PankajaBalasooriya/SLRC-2025-Pulztrones/Designs/3D Prints/Part P.STL

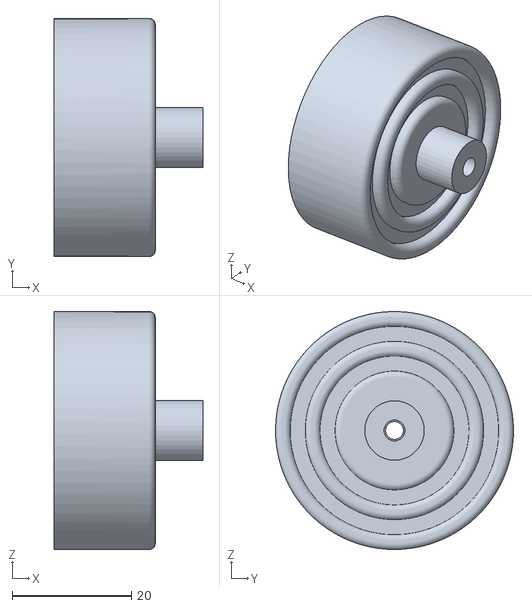
[picture p26: CAD file, 2025-03-19]
Designs/3D Prints/Part P.STL
25.0 x 40.0 x 40.0
