PankajaBalasooriya/SLRC-2025-Pulztrones/Designs/Laser Cuts/Bottom-plate.DXF

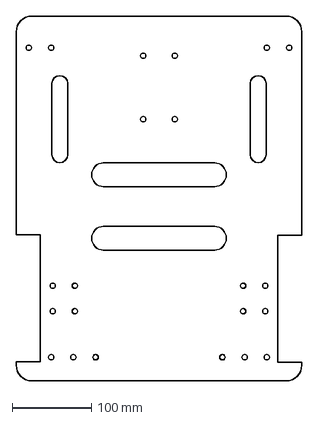
[picture p27: CAD file, 2025-03-19]
Designs/Laser Cuts/Bottom-plate.DXF
360.0 x 460.0 mm
