PankajaBalasooriya/SLRC-2025-Pulztrones/Designs/Mian Design/Bottom Base Plate.SLDPRT

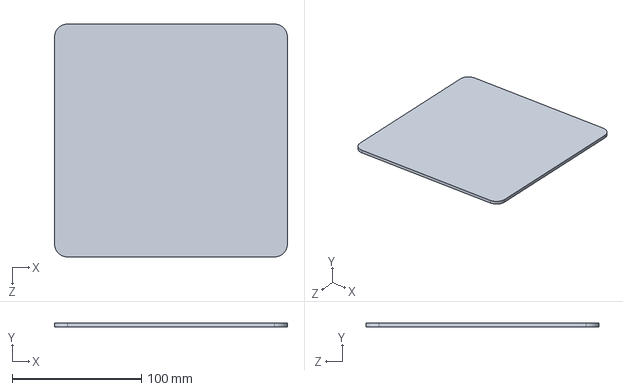
[picture p28: CAD file, 2025-03-19]
Designs/Mian Design/Bottom Base Plate.SLDPRT
180.0 x 3.00 x 180.0 mm
