PankajaBalasooriya/SLRC-2025-Pulztrones/Designs/Arm design/Part1.SLDPRT

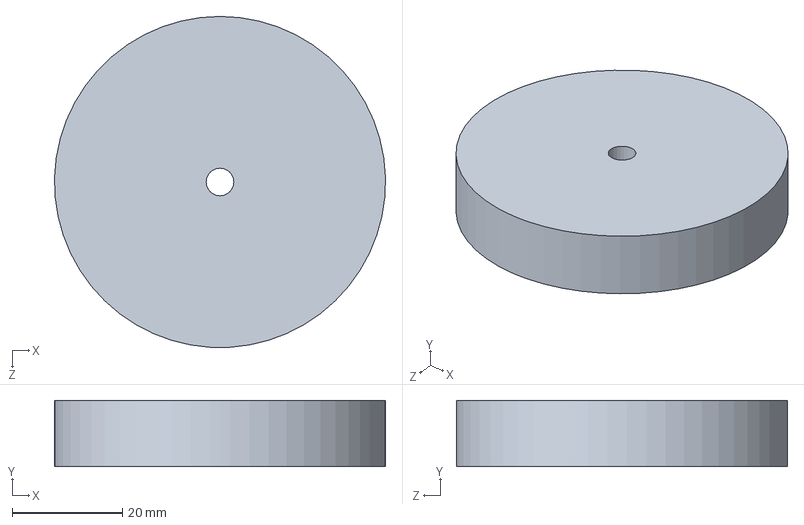
[picture p29: CAD file, 2025-03-19]
Designs/Arm design/Part1.SLDPRT
60.0 x 12.0 x 60.0 mm
