PankajaBalasooriya/SLRC-2025-Pulztrones/Designs/Laser Cuts/Mid-plate.DXF

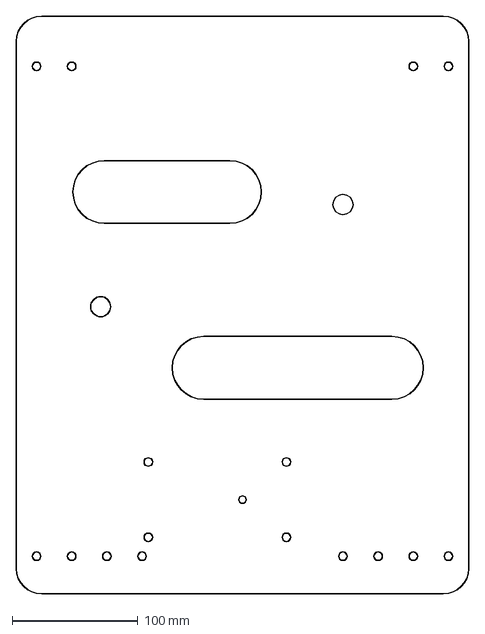
[picture p30: CAD file, 2025-03-19]
Designs/Laser Cuts/Mid-plate.DXF
360.0 x 460.0 mm
