PankajaBalasooriya/SLRC-2025-Pulztrones/Designs/Mian Design/Mid-plate.SLDPRT

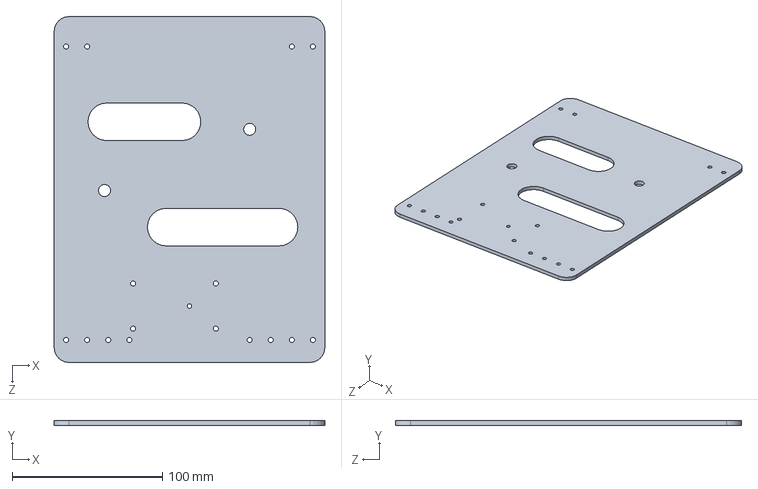
[picture p31: CAD file, 2025-03-19]
Designs/Mian Design/Mid-plate.SLDPRT
180.0 x 3.00 x 230.0 mm
