PankajaBalasooriya/SLRC-2025-Pulztrones/Designs/3D Prints/small servo mount.STL

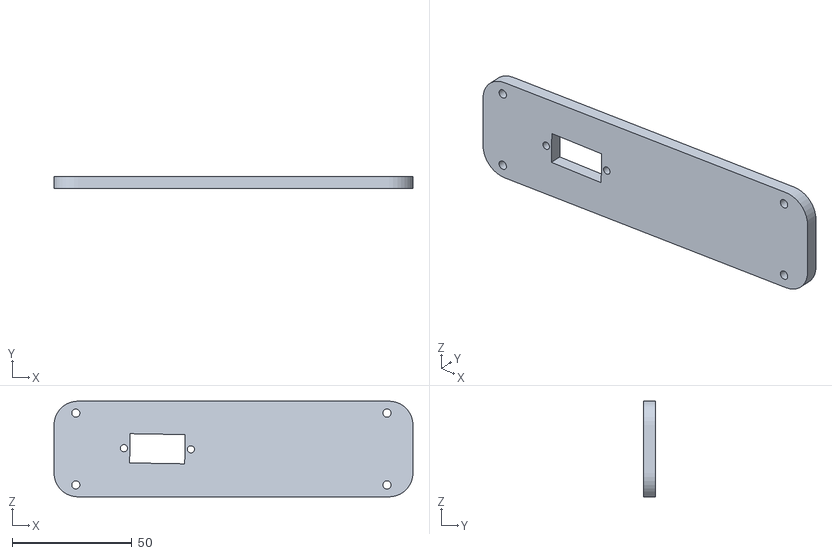
[picture p32: CAD file, 2025-03-19]
Designs/3D Prints/small servo mount.STL
150.0 x 5.00 x 40.0
