PankajaBalasooriya/SLRC-2025-Pulztrones/Designs/Arm design/part B.SLDPRT

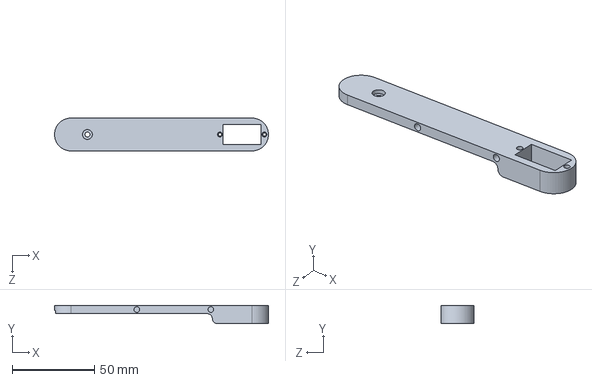
[picture p33: CAD file, 2025-03-19]
Designs/Arm design/part B.SLDPRT
130.0 x 11.0 x 20.0 mm
