PankajaBalasooriya/SLRC-2025-Pulztrones/Designs/Arm design/Part J.SLDPRT

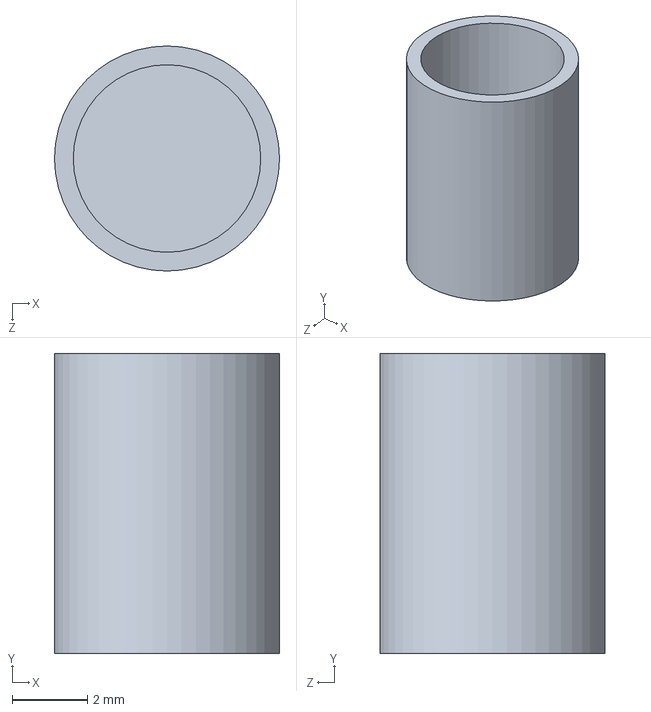
[picture p35: CAD file, 2025-03-19]
Designs/Arm design/Part J.SLDPRT
6.00 x 8.00 x 6.00 mm
