PankajaBalasooriya/SLRC-2025-Pulztrones/Designs/Mian Design/Top-plate.SLDPRT

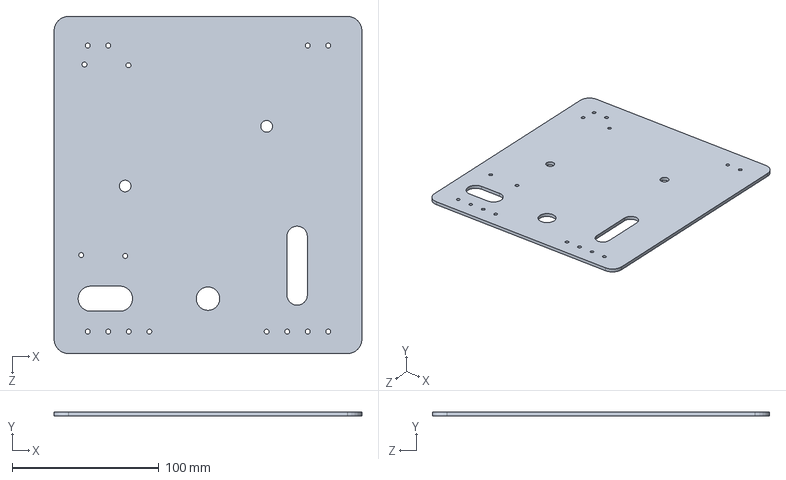
[picture p36: CAD file, 2025-03-19]
Designs/Mian Design/Top-plate.SLDPRT
210.0 x 3.00 x 230.0 mm
