PankajaBalasooriya/SLRC-2025-Pulztrones/Designs/Arm design/big servo holder.SLDPRT

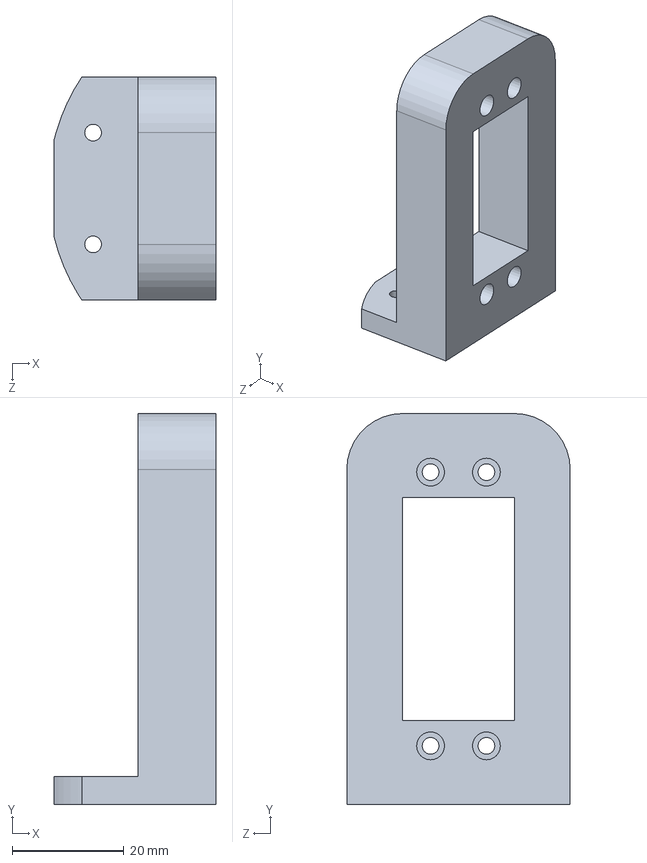
[picture p37: CAD file, 2025-03-19]
Designs/Arm design/big servo holder.SLDPRT
29.0 x 70.0 x 40.0 mm
