PankajaBalasooriya/SLRC-2025-Pulztrones/Designs/Mian Design/mid low plate.SLDPRT

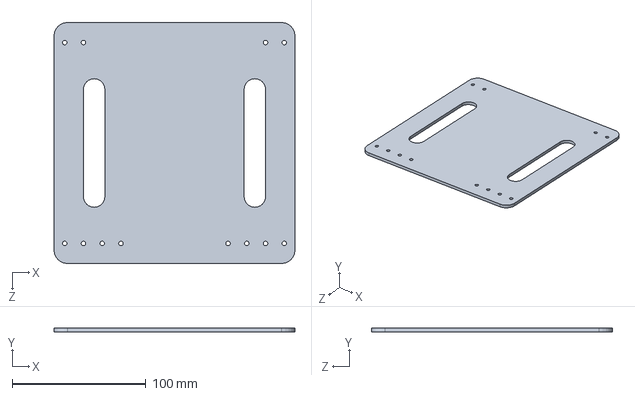
[picture p38: CAD file, 2025-03-19]
Designs/Mian Design/mid low plate.SLDPRT
180.0 x 3.00 x 180.0 mm
