PankajaBalasooriya/SLRC-2025-Pulztrones/Designs/Arm design/part N.SLDPRT

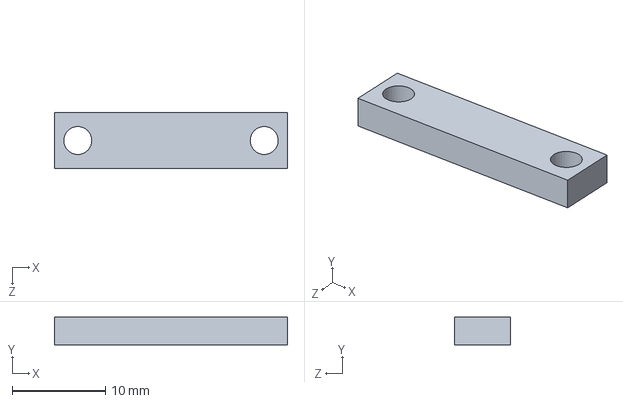
[picture p39: CAD file, 2025-03-19]
Designs/Arm design/part N.SLDPRT
25.0 x 3.00 x 6.00 mm
