PankajaBalasooriya/SLRC-2025-Pulztrones/Designs/Ball Storage/mg996_arm_2pad.step.SLDPRT

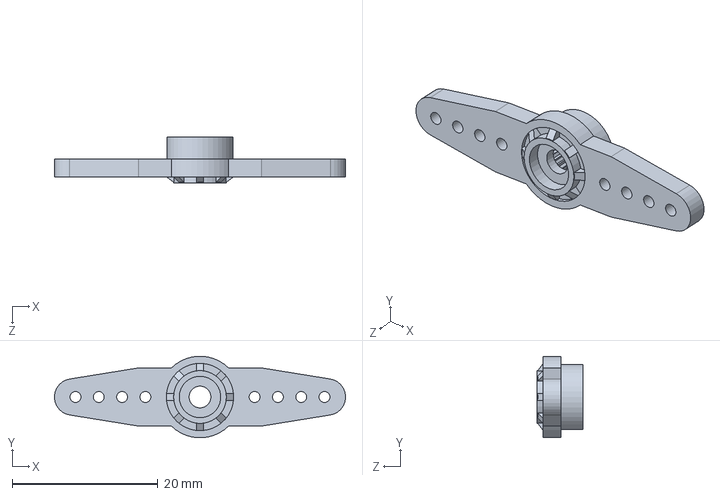
[picture p40: CAD file, 2025-03-19]
Designs/Ball Storage/mg996_arm_2pad.step.SLDPRT
40.0 x 11.2 x 6.30 mm
