PankajaBalasooriya/SLRC-2025-Pulztrones/Designs/3D Prints/spur gear_ai_with servo_connecton.STL

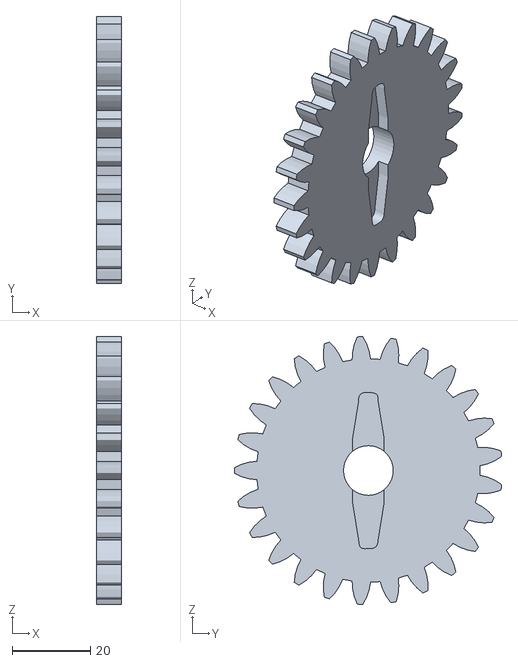
[picture p41: CAD file, 2025-03-19]
Designs/3D Prints/spur gear_ai_with servo_connecton.STL
6.35 x 68.4 x 68.5
