PankajaBalasooriya/SLRC-2025-Pulztrones/Designs/Arm design/part D.SLDPRT

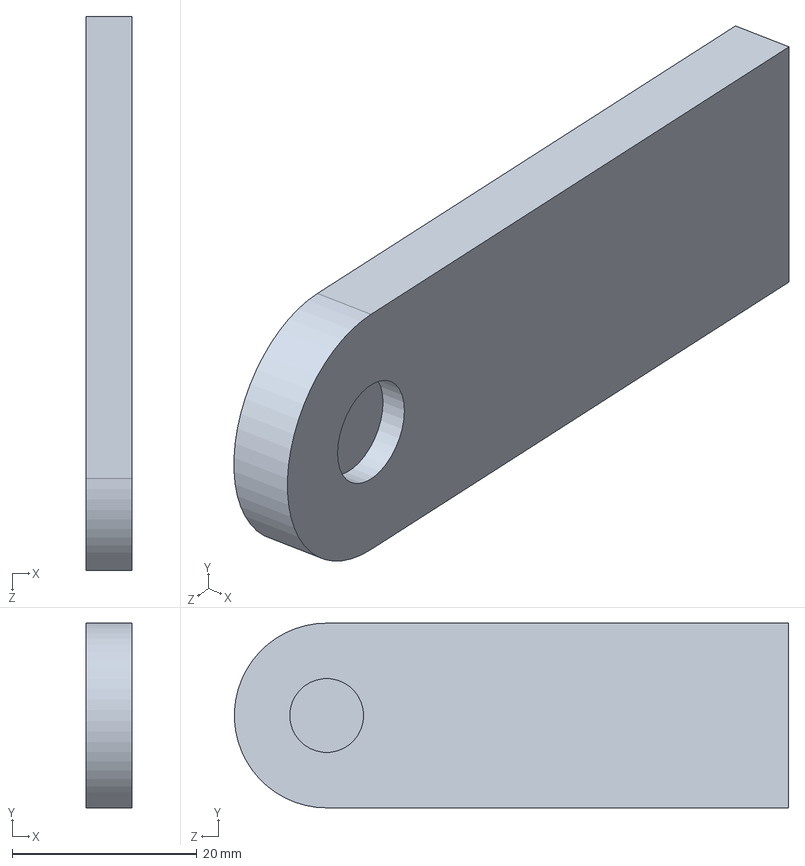
[picture p42: CAD file, 2025-03-19]
Designs/Arm design/part D.SLDPRT
5.00 x 20.0 x 60.0 mm
