PankajaBalasooriya/SLRC-2025-Pulztrones/Designs/3D Prints/Coupling Gear - spur gear_ai-2.STL

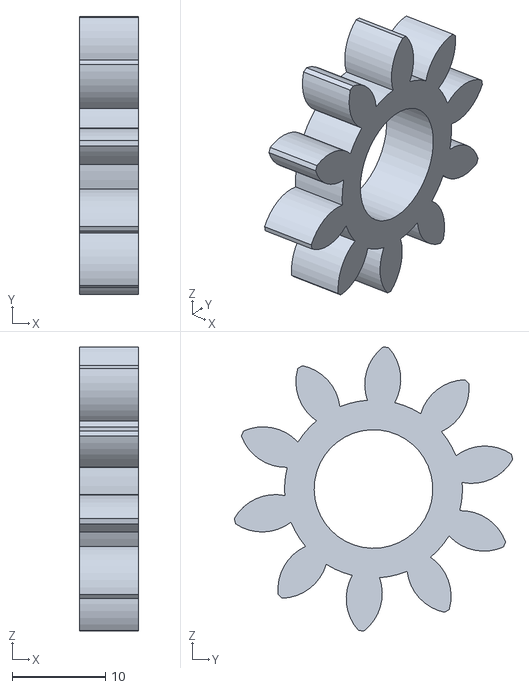
[picture p43: CAD file, 2025-03-19]
Designs/3D Prints/Coupling Gear - spur gear_ai-2.STL
6.35 x 29.8 x 30.4
