PankajaBalasooriya/SLRC-2025-Pulztrones/Designs/Arm design/base.SLDPRT

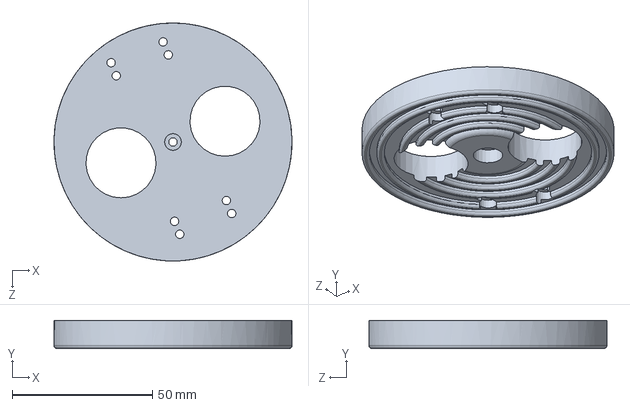
[picture p44: CAD file, 2025-03-19]
Designs/Arm design/base.SLDPRT
85.0 x 10.0 x 85.0 mm
