PankajaBalasooriya/SLRC-2025-Pulztrones/Designs/Arm design/Part I.SLDPRT

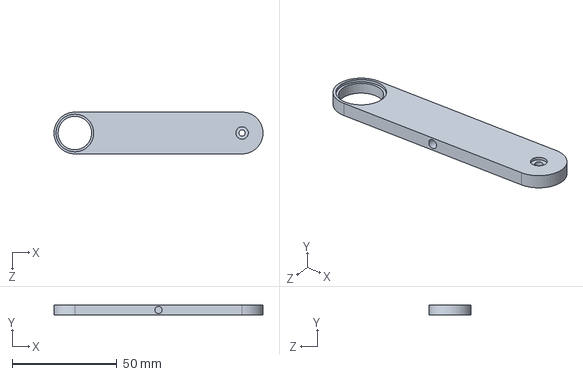
[picture p45: CAD file, 2025-03-19]
Designs/Arm design/Part I.SLDPRT
100.0 x 5.00 x 20.0 mm
