PankajaBalasooriya/SLRC-2025-Pulztrones/Designs/Ball Storage/gear bearing shaft.SLDPRT

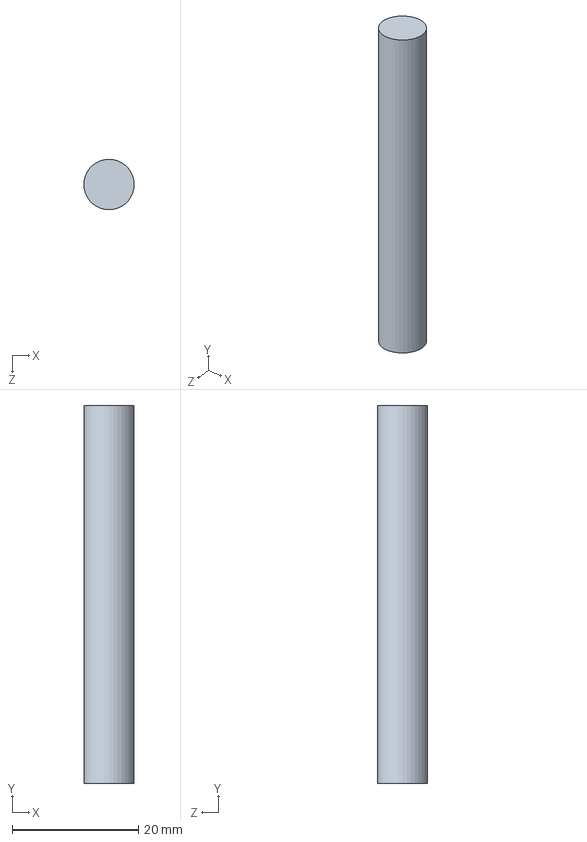
[picture p46: CAD file, 2025-03-19]
Designs/Ball Storage/gear bearing shaft.SLDPRT
8.00 x 60.0 x 8.00 mm
