PankajaBalasooriya/SLRC-2025-Pulztrones/Designs/Arm design/part F.SLDPRT

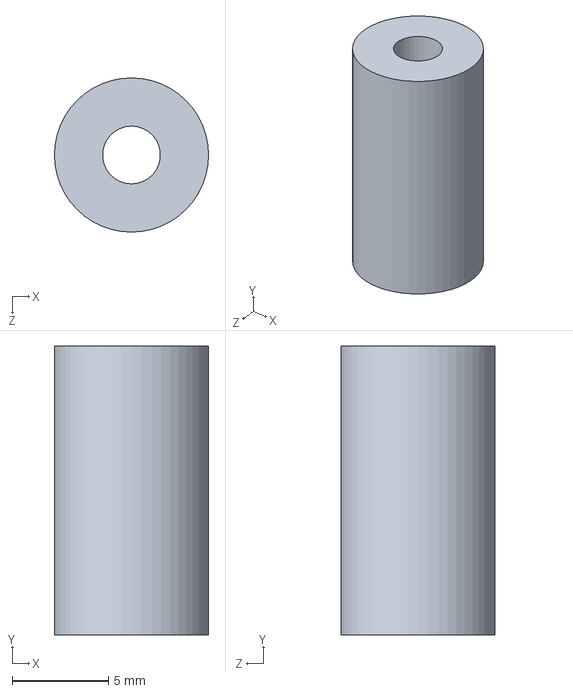
[picture p47: CAD file, 2025-03-19]
Designs/Arm design/part F.SLDPRT
8.00 x 15.0 x 8.00 mm
