PankajaBalasooriya/SLRC-2025-Pulztrones/Designs/Ball Storage/Storage Gear.SLDPRT

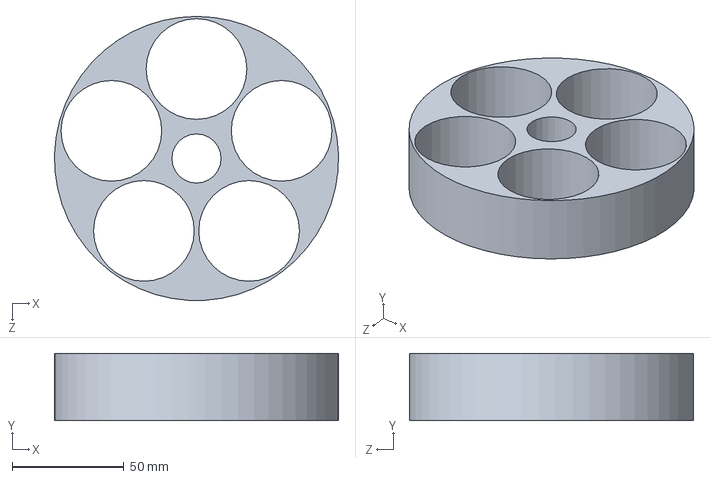
[picture p48: CAD file, 2025-03-19]
Designs/Ball Storage/Storage Gear.SLDPRT
126.9 x 30.0 x 127.0 mm
