PankajaBalasooriya/SLRC-2025-Pulztrones/Designs/Arm design/Part L.SLDPRT

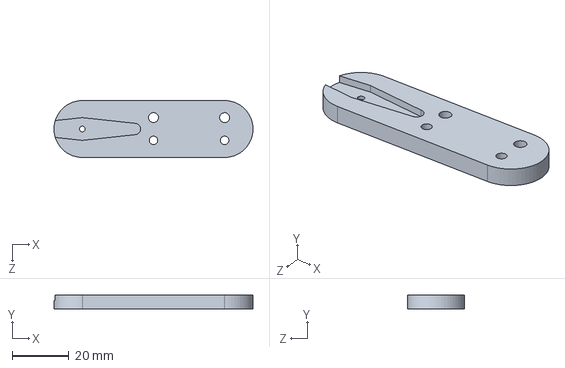
[picture p49: CAD file, 2025-03-19]
Designs/Arm design/Part L.SLDPRT
70.0 x 5.00 x 20.0 mm
