PankajaBalasooriya/SLRC-2025-Pulztrones/Designs/Ball Storage/Pop up Gear.SLDPRT

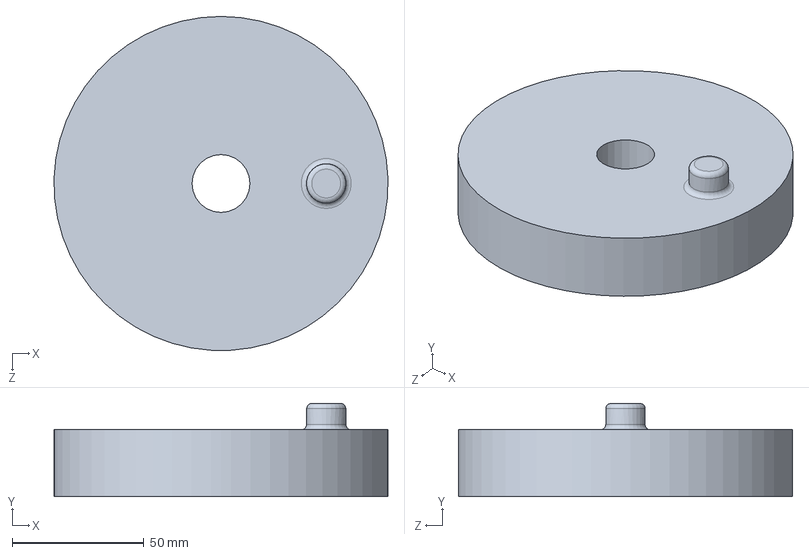
[picture p50: CAD file, 2025-02-25]
Designs/Ball Storage/Pop up Gear.SLDPRT
126.9 x 35.4 x 127.0 mm
