PankajaBalasooriya/SLRC-2025-Pulztrones/Designs/Arm design/part A.SLDPRT

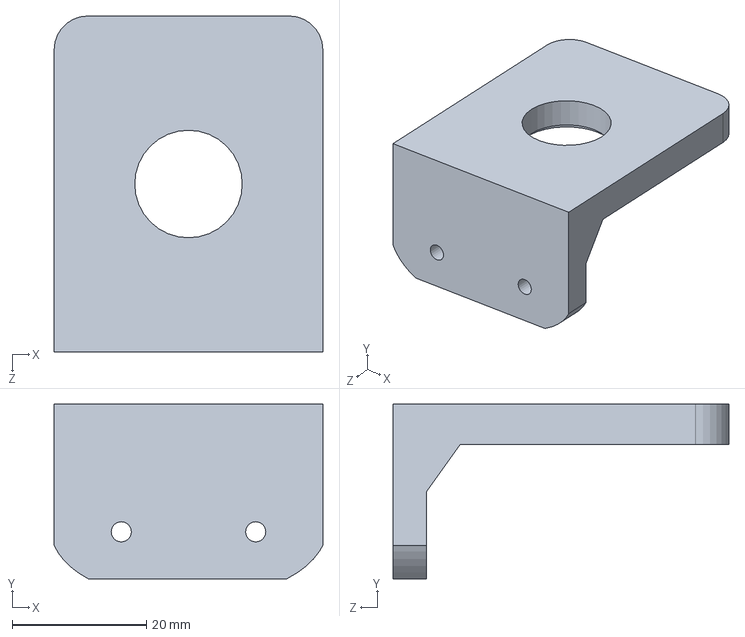
[picture p51: CAD file, 2025-03-19]
Designs/Arm design/part A.SLDPRT
40.0 x 26.0 x 50.0 mm
