PankajaBalasooriya/SLRC-2025-Pulztrones/Designs/Ball Storage/vertical servo mount high gear.SLDPRT

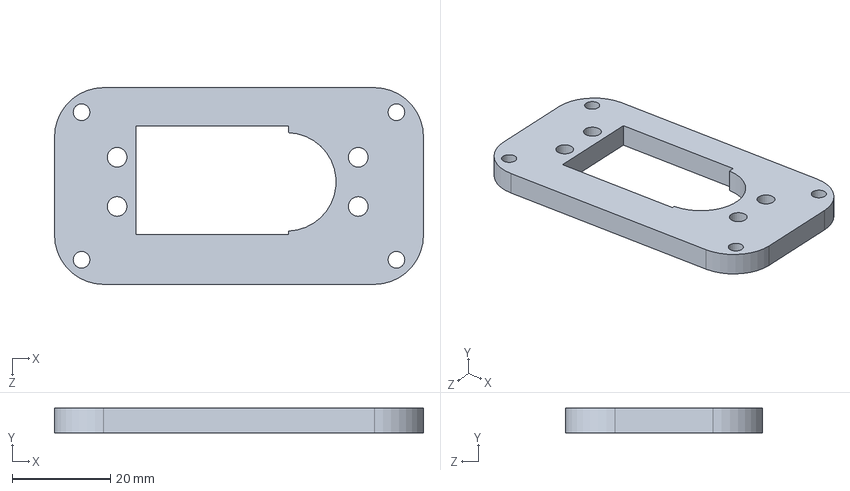
[picture p52: CAD file, 2025-02-25]
Designs/Ball Storage/vertical servo mount high gear.SLDPRT
75.0 x 5.00 x 40.0 mm
