PankajaBalasooriya/SLRC-2025-Pulztrones/Designs/Ball Storage/mg996R_v2.step.SLDPRT

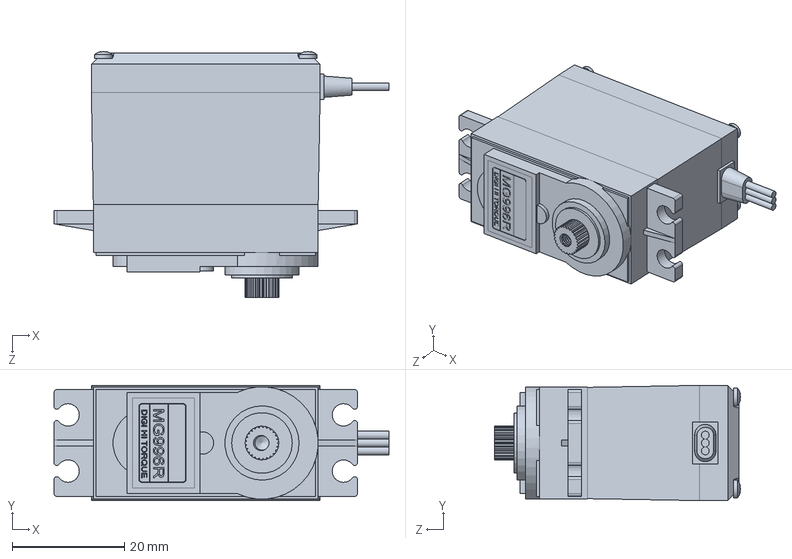
[picture p53: CAD file, 2025-02-23]
Designs/Ball Storage/mg996R_v2.step.SLDPRT
59.6 x 20.5 x 43.8 mm
