PankajaBalasooriya/SLRC-2025-Pulztrones/Designs/Arm design/camera holder.SLDPRT

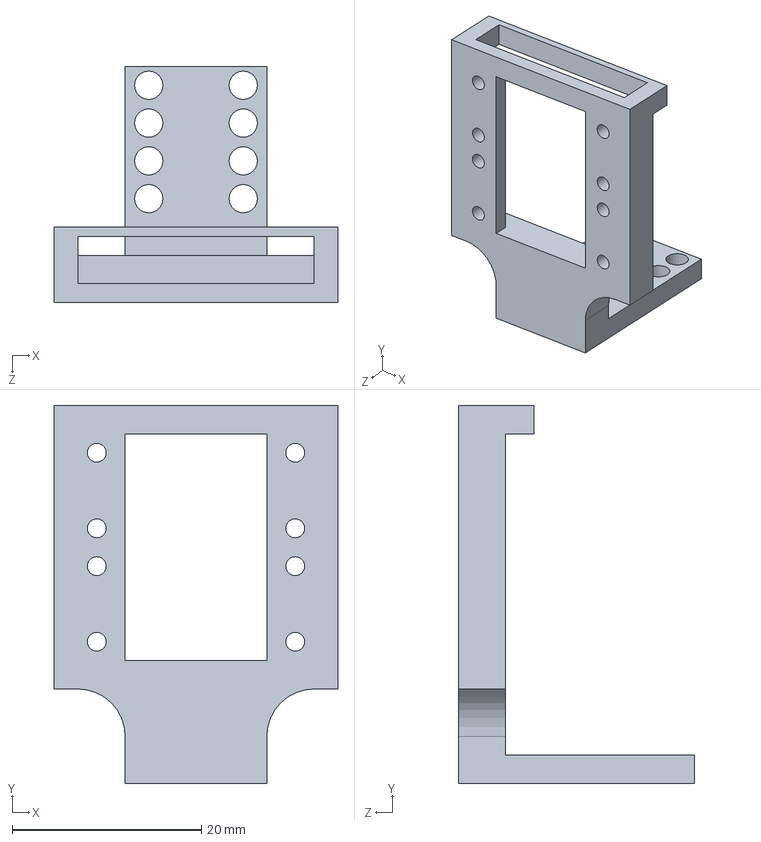
[picture p54: CAD file, 2025-03-19]
Designs/Arm design/camera holder.SLDPRT
30.0 x 40.0 x 25.0 mm
