PankajaBalasooriya/SLRC-2025-Pulztrones/Designs/Arm design/big servo holder 2.SLDPRT

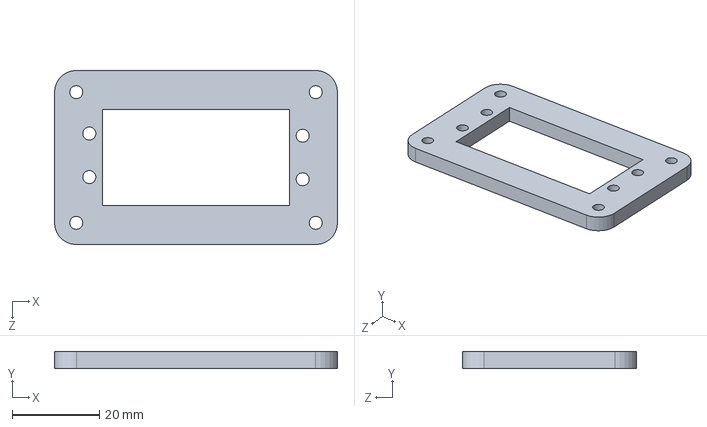
[picture p55: CAD file, 2025-03-19]
Designs/Arm design/big servo holder 2.SLDPRT
65.0 x 4.00 x 40.0 mm
