PankajaBalasooriya/SLRC-2025-Pulztrones/Designs/Ball Storage/Servo mount new.SLDPRT

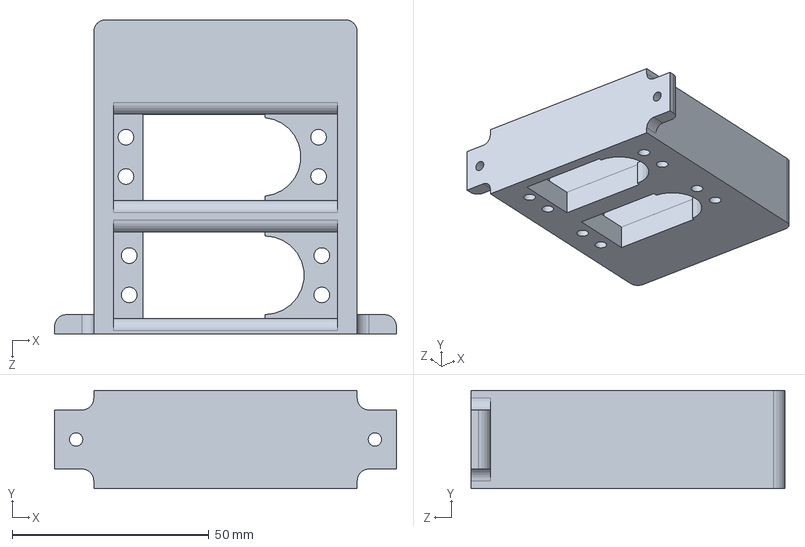
[picture p56: CAD file, 2025-02-23]
Designs/Ball Storage/Servo mount new.SLDPRT
87.0 x 25.0 x 80.0 mm
