PankajaBalasooriya/SLRC-2025-Pulztrones/Designs/Arm design/Part G.SLDPRT

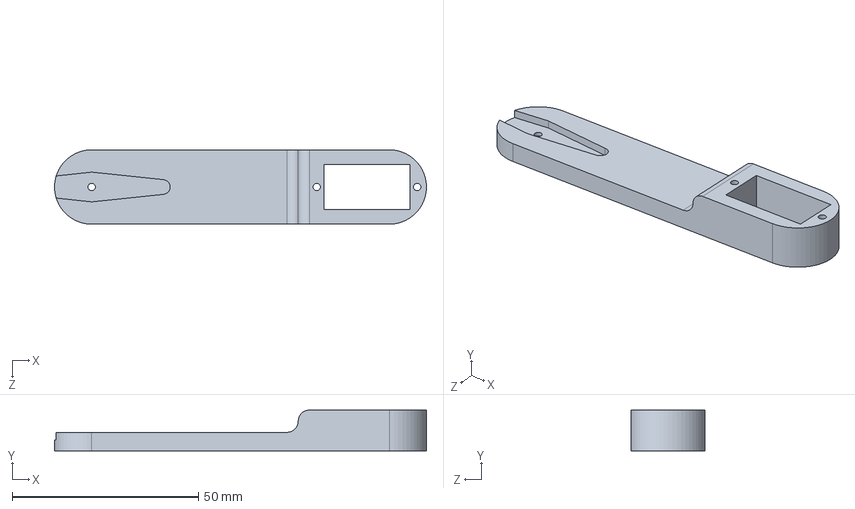
[picture p57: CAD file, 2025-03-19]
Designs/Arm design/Part G.SLDPRT
100.0 x 11.0 x 20.0 mm
