PankajaBalasooriya/SLRC-2025-Pulztrones/Designs/Arm design/part C.SLDPRT

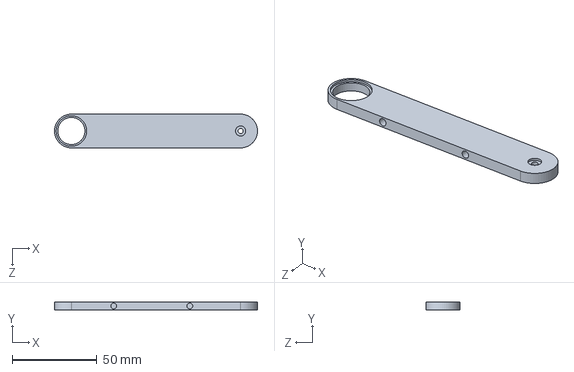
[picture p58: CAD file, 2025-03-19]
Designs/Arm design/part C.SLDPRT
120.0 x 5.00 x 20.0 mm
