PankajaBalasooriya/SLRC-2025-Pulztrones/Designs/Arm design/part K.SLDPRT

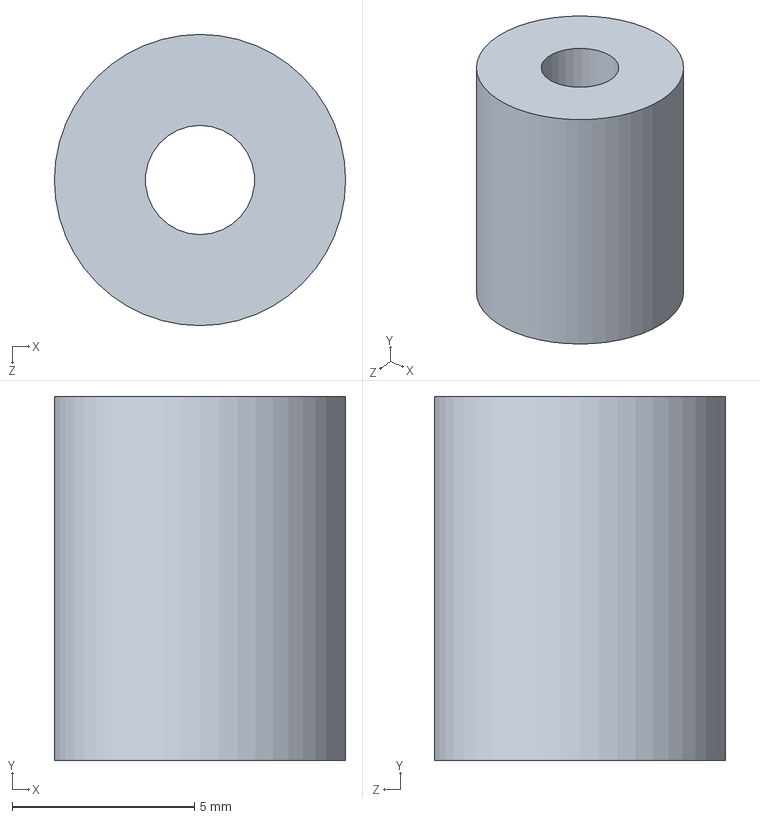
[picture p59: CAD file, 2025-03-19]
Designs/Arm design/part K.SLDPRT
8.00 x 10.0 x 8.00 mm
