PankajaBalasooriya/SLRC-2025-Pulztrones/Designs/Arm design/part M.SLDPRT

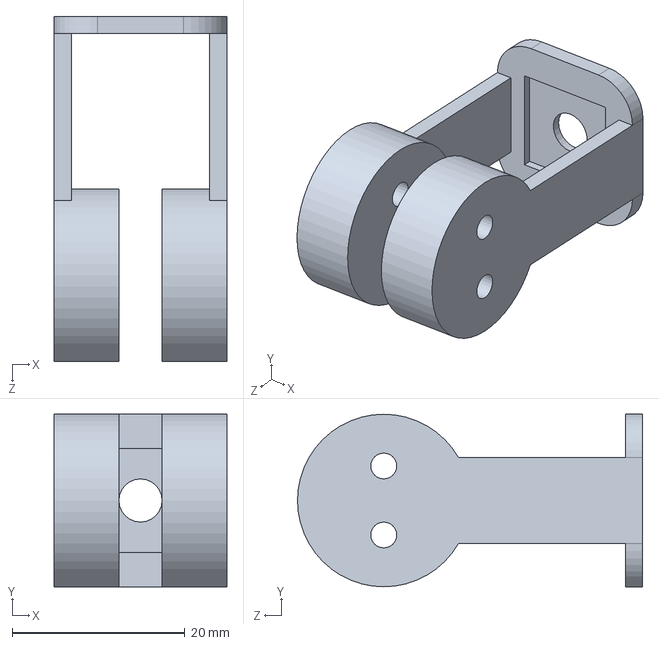
[picture p60: CAD file, 2025-03-19]
Designs/Arm design/part M.SLDPRT
20.0 x 20.0 x 40.0 mm
