PankajaBalasooriya/SLRC-2025-Pulztrones/software/firmware/SLRC2025-Pulztrones/Core/Src/config.c

#include "config.h"
#include "buzzer.h"
#include "stm32f4xx.h"
#include "main.h"
#include <stdio.h>

//*** Robot state **********************************************//

volatile State RobotState = None;
//***************************************************************************//


const float ROBOT_RADIUS = 93.50;  // Adjust to your Robot specs - 93.25
const float DEG_PER_MM_DIFFERENCE = (180.0 / (2 * ROBOT_RADIUS * PI));
const float RADIANS_PER_DEGREE = 0.01746031746031746031746031746032;
const float DEGREES_PER_RADIAN = 57.295779513082320876798154814105;




//*** MOTION CONTROLLER CONSTANTS **********************************************//
const float LOOP_FREQUENCY = 50;
const float LOOP_INTERVAL = 0.02;

//need to adjust kp and kd values for required velocity and acceleration values
//const float FWD_KP = 0.005;// 0.045
//const float FWD_KD = 0.1;// 0.5

//const float ROT_KP = 0.017; //0.009
//const float ROT_KD = 0.1;

// Dynamic performance constants
// There is a video describing how to get these numbers and calculate the feedforward
// constants here: https://youtu.be/BrabDeHGsa0
const float FWD_KM = 977.54;  /// *
const float FWD_TM = 0.2569;  ///*0.00090 forward time constant 63%

const float ROT_KM = 595.55;  //* deg/s/Volt
const float ROT_TM = 0.1660;  ///* rotation time constant

const float SPEED_FF = (1.0 / FWD_KM);
const float ACC_FF = (FWD_TM / FWD_KM);
const float BIAS_FF = 0.1815884772; // *

// forward motion controller constants
const float FWD_ZETA = 0.707;
const float FWD_TD = FWD_TM;

const float FWD_KP = 16 * FWD_TM / (FWD_KM * FWD_ZETA * FWD_ZETA * FWD_TD * FWD_TD);
const float FWD_KD = LOOP_FREQUENCY * (8 * FWD_TM - FWD_TD) / (FWD_KM * FWD_TD);

// rotation motion controller constants
const float ROT_ZETA = 0.707;
const float ROT_TD = ROT_TM;

const float ROT_KP = 16 * ROT_TM / (ROT_KM * ROT_ZETA * ROT_ZETA * ROT_TD * ROT_TD);
const float ROT_KD = LOOP_FREQUENCY * (8 * ROT_TM - ROT_TD) / (ROT_KM * ROT_TD);


// controller constants for the steering controller
const float STEERING_KP = 0.001;//0.003
const float STEERING_KD = 0.00001; ///0.00001
const float STEERING_FRONT_KP = 0.02;
const float STEERING_FRONT_KD = 0.0001;
const float STEERING_ADJUST_LIMIT = 0.6;  // deg/s

//***************************************************************************//


//***** PERFORMANCE CONSTANTS************************************************//
const int LINE_FOLLOW_SPEED = 85;
const int LINE_FOLLOW_ACCELERATION = 120;

const int FORWARD_SPEED_1 = 100;
const int FORWARD_ACCELERATION_1 = 120;

const int FORWARD_SPEED_2 = 30;
const int FORWARD_ACCELERATION_2 = 10;


const int SPIN_TURN_OMEGA = 150;
const int SPIN_TURN_ALPHA = 50;




//***** SENSOR SCALING ******************************************************//
// This is the normalised value seen by the front sensor when the Robot is
// in its calibration positio8
const int SIDE_NOMINAL = 90;//-
const int FRONT_NOMINAL = 80;

// the values above which, a wall is seen
const int LEFT_THRESHOLD = 80;   // minimum value to register a wall
const int RIGHT_THRESHOLD = 80;  // minimum value to register a wall
const int FRONT_THRESHOLD = 75;  // minimum value to register a wall-


const int WALL_ANGLE_WEIGHT = 0.1;


//***** Robot constants ******************************************************//

const int MOTION_DELAY = 800;
const int DISTACE_TO_CENTER_OF_CELL = 153; //150

//***** Box manupilation constants ******************************************************//
const int BOX_THRESHOLD = 50; // minimum value to register a box


//***** Pump Controlling functions ******************************************************//

void turn_on_water_pump(){
	HAL_GPIO_WritePin(WATERPUMP_GPIO_Port, WATERPUMP_Pin, 0);
}

void turn_off_water_pump(){
	HAL_GPIO_WritePin(WATERPUMP_GPIO_Port, WATERPUMP_Pin, 1);
}

void turn_on_air_pump(){
	HAL_GPIO_WritePin(AIRPUMP_GPIO_Port, AIRPUMP_Pin, 0);
}

void turn_off_air_pump(){
	HAL_GPIO_WritePin(AIRPUMP_GPIO_Port, AIRPUMP_Pin, 1);
}



//****** Button Handler ***************************************************************************
volatile uint32_t previousMillis = 0;
volatile uint32_t currentMillis = 0;

volatile uint32_t okbtncount = 0;
volatile uint32_t prevokbtncount = 0;

volatile uint32_t nextbtncount = 1;
volatile uint32_t prevnextbtncount = 0;

void HAL_GPIO_EXTI_Callback(uint16_t GPIO_Pin) {
	currentMillis = HAL_GetTick();
    if (GPIO_Pin == B1_Pin && (currentMillis - previousMillis > 650))  // Replace BUTTON_PIN with actual GPIO pin
	{
    	nextbtncount++; // Set flag when button is pressed
		//Buzzer_On();
	}
    else if (GPIO_Pin == GPIO_PIN_11 && (currentMillis - previousMillis > 650)){
    	okbtncount++;
    }

    previousMillis = currentMillis;
}

void Reset_buttons(){
	okbtncount = 0;
	prevokbtncount = 0;

	nextbtncount = 0;
	prevnextbtncount = 0;
}



int binaryToDecimal4Bit(int binaryArray[]) {
    // For 4-bit number where index 0 is the least significant bit
    return binaryArray[0] * 1 +    // 2^0 = 1
           binaryArray[1] * 2 +    // 2^1 = 2
           binaryArray[2] * 4 +    // 2^2 = 4
           binaryArray[3] * 8;     // 2^3 = 8
}

// Returns 0 if number is odd, 1 if even
int isEven(int number) {
    return !(number % 2);
}
