PankajaBalasooriya/SLRC-2025-Pulztrones/software/firmware/SLRC2025-Pulztrones/Core/Inc/main.h

#define B1_Pin GPIO_PIN_13
#define B1_GPIO_Port GPIOC
#define B1_EXTI_IRQn EXTI15_10_IRQn
#define IR_ADC_Pin GPIO_PIN_0
#define IR_ADC_GPIO_Port GPIOC
#define AIRPUMP_Pin GPIO_PIN_1
#define AIRPUMP_GPIO_Port GPIOC
#define WATERPUMP_Pin GPIO_PIN_2
#define WATERPUMP_GPIO_Port GPIOC
#define RightEncoderCh1_Pin GPIO_PIN_0
#define RightEncoderCh1_GPIO_Port GPIOA
#define RightEncoderCh2_Pin GPIO_PIN_1
#define RightEncoderCh2_GPIO_Port GPIOA
#define USART_TX_Pin GPIO_PIN_2
#define USART_TX_GPIO_Port GPIOA
#define USART_RX_Pin GPIO_PIN_3
#define USART_RX_GPIO_Port GPIOA
#define LD2_Pin GPIO_PIN_5
#define LD2_GPIO_Port GPIOA
#define S0_Pin GPIO_PIN_12
#define S0_GPIO_Port GPIOB
#define S1_Pin GPIO_PIN_13
#define S1_GPIO_Port GPIOB
#define S2_Pin GPIO_PIN_14
#define S2_GPIO_Port GPIOB
#define S3_Pin GPIO_PIN_15
#define S3_GPIO_Port GPIOB
#define LeftEncoderCh1_Pin GPIO_PIN_8
#define LeftEncoderCh1_GPIO_Port GPIOA
#define LeftEncoderCh2_Pin GPIO_PIN_9
#define LeftEncoderCh2_GPIO_Port GPIOA
#define TMS_Pin GPIO_PIN_13
#define TMS_GPIO_Port GPIOA
#define TCK_Pin GPIO_PIN_14
#define TCK_GPIO_Port GPIOA
#define SWO_Pin GPIO_PIN_3
#define SWO_GPIO_Port GPIOB
