PankajaBalasooriya/SLRC-2025-Pulztrones/software/firmware/SLRC2025-Pulztrones/Core/Inc/robot.h

/**
  ******************************************************************************
  * @file           : robot.h
  * @brief          : Header for robot_control.c file.
  *                   This file contains the function prototypes
  *                   for robot control operations.
  ******************************************************************************
  */

#ifndef __ROBOT_H
#define __ROBOT_H

#ifdef __cplusplus
extern "C" {
#endif

/* Includes ------------------------------------------------------------------*/
#include "stm32f4xx_hal.h"
#include "config.h"

// In robot.h
extern int colorcounter;
extern volatile Color linecolorRPI;
extern volatile Color ballcolorRPI;

/* Exported types ------------------------------------------------------------*/
/* Exported constants --------------------------------------------------------*/
/* Exported macro ------------------------------------------------------------*/
/* Exported functions prototypes ---------------------------------------------*/
void HandleLineDetection(uint8_t *data);
void HandleGridPosition(uint8_t *data);
void HandleColorDetection(uint8_t *data);
void StopRobot(void);
void HandleLineColorDetection(uint8_t *data);


//Dummy functions
Color GetLineColor(uint8_t column, uint8_t row);
//Color GetLineColor();
//Color GetBallColor(uint8_t column, uint8_t row);
Color GetBallColor();



JunctionType Robot_LineFollowUntillJunction();
JunctionType Robot_LineFollowUntillJunctionAndNotStop();
void Robot_FollowLineGivenDistance(int distnace);
void Robot_MoveReverseGivenDistanceSLOW(int distnace);
void Robot_MoveForwardGivenDistanceSLOW(int distnace);
void Robot_FollowLineGivenDistanceandNotStop(int distnace);
JunctionType Robot_MoveForwardUntillLine();
void Robot_MoveForwardGivenDistance(int distnace);
void Robot_MoveReverseGivenDistance(int distnace);
void Robot_TurnRight90Inplace();
void Robot_TurnLeft90Inplace();
void robot_TurnRight180Inplace();
float Robot_moveForwardUntillFrontWall();
void Robot_adjust_using_front_wall();
void Robot_TurnLeftInplace(float angle);
void Robot_TurnRightInplace(float angle);
int Robot_moveForwardUntillBox(uint16_t input_distance);

uint8_t Robot_read_Barcode();


#ifdef __cplusplus
}
#endif

#endif /* __ROBOT_H */
