PankajaBalasooriya/SLRC-2025-Pulztrones/software/firmware/SLRC2025-Pulztrones/Core/Inc/encoders.h

/*
 * encoders.h
 */

#ifndef INC_ENCODERS_H_
#define INC_ENCODERS_H_

int16_t getRightEncoderCounts();
int16_t getLeftEncoderCounts();
void resetEncoders();


void resetEncodersinSystick();

void update_Encoder_Data();
float robot_distance();

float robot_speed();

float robot_omega();

float robot_fwd_change();
float robot_rot_change();

float robot_angle();

#endif /* INC_ENCODERS_H_ */
