PankajaBalasooriya/SLRC-2025-Pulztrones/software/firmware/SLRC2025-Pulztrones/Drivers/Buzzer/Src/buzzer.c

#include "buzzer.h"
#include "main.h"

// Turn on the buzzer (PC15 high)
void Buzzer_On(void)
{
    HAL_GPIO_WritePin(GPIOA, GPIO_PIN_5, GPIO_PIN_SET);
}

// Turn off the buzzer (PC15 low)
void Buzzer_Off(void)
{
    HAL_GPIO_WritePin(GPIOA, GPIO_PIN_5, GPIO_PIN_RESET);
}

// Toggle the buzzer state with a specified delay
void Buzzer_Toggle(uint32_t delay)
{
    Buzzer_On();
    HAL_Delay(delay);
    Buzzer_Off();
    HAL_Delay(delay);
}

void Buzzer_UniquePattern(void)
{
    // Pattern: Short-Short-Long-Short-Long
    // Total duration: 1000ms (1 second)

    Buzzer_On();
    HAL_Delay(100);  // 100ms on
    Buzzer_Off();
    HAL_Delay(100);  // 100ms off

    Buzzer_On();
    HAL_Delay(100);  // 100ms on
    Buzzer_Off();
    HAL_Delay(100);  // 100ms off

    Buzzer_On();
    HAL_Delay(200);  // 200ms on
    Buzzer_Off();
    HAL_Delay(100);  // 100ms off

    Buzzer_On();
    HAL_Delay(100);  // 100ms on
    Buzzer_Off();
    HAL_Delay(100);  // 100ms off

    Buzzer_On();
    HAL_Delay(200);  // 200ms on
    Buzzer_Off();
    // No delay at the end to make it exactly 1 second
}


void Buzzer_TaskCompletion(void)
{
    // Triumphant rising pattern (approximately 1.2 seconds)

    // Initial quick triple beep
    for (int i = 0; i < 3; i++) {
        Buzzer_On();
        HAL_Delay(50);  // 50ms on
        Buzzer_Off();
        HAL_Delay(50);  // 50ms off
    }

    // Rising tones effect (achieved with different durations)
    Buzzer_On();
    HAL_Delay(100);  // Short tone
    Buzzer_Off();
    HAL_Delay(50);

    Buzzer_On();
    HAL_Delay(150);  // Medium tone
    Buzzer_Off();
    HAL_Delay(50);

    Buzzer_On();
    HAL_Delay(200);  // Longer tone
    Buzzer_Off();
    HAL_Delay(50);

    // Final celebratory long tone
    Buzzer_On();
    HAL_Delay(300);  // Longest tone
    Buzzer_Off();
}


void Buzzer_ErrorPattern(void)
{
    // Three short beeps
    for (int i = 0; i < 3; i++) {
        Buzzer_On();
        HAL_Delay(100);
        Buzzer_Off();
        HAL_Delay(100);
    }

    // Three long beeps
    for (int i = 0; i < 3; i++) {
        Buzzer_On();
        HAL_Delay(300);
        Buzzer_Off();
        HAL_Delay(100);
    }

    // Three short beeps again
    for (int i = 0; i < 3; i++) {
        Buzzer_On();
        HAL_Delay(100);
        Buzzer_Off();
        HAL_Delay(100);
    }

    // 1-second pause before repeating
    HAL_Delay(1000);
}
