PankajaBalasooriya/SLRC-2025-Pulztrones/software/firmware/SLRC2025-Pulztrones/Drivers/TCS3472/Inc/TCS3472.h

/**
 * @file tcs3472.h
 * @brief TCS3472 Color Sensor Driver Header
 */

#ifndef TCS3472_H
#define TCS3472_H

#include <stdint.h>
#include "main.h"
#include "PCA9548A.h"  // Include your i2c_mux header
#include "config.h"

/* TCS3472 I2C Address */
#define TCS3472_ADDR                 (0x29 << 1)  // 7-bit address shifted left

/* TCS3472 Registers */
#define TCS3472_COMMAND_BIT          0x80
#define TCS3472_REG_ENABLE           0x00
#define TCS3472_REG_ATIME            0x01
#define TCS3472_REG_WTIME            0x03
#define TCS3472_REG_AILTL            0x04
#define TCS3472_REG_AILTH            0x05
#define TCS3472_REG_AIHTL            0x06
#define TCS3472_REG_AIHTH            0x07
#define TCS3472_REG_PERS             0x0C
#define TCS3472_REG_CONFIG           0x0D
#define TCS3472_REG_CONTROL          0x0F
#define TCS3472_REG_ID               0x12
#define TCS3472_REG_STATUS           0x13
#define TCS3472_REG_CDATAL           0x14
#define TCS3472_REG_CDATAH           0x15
#define TCS3472_REG_RDATAL           0x16
#define TCS3472_REG_RDATAH           0x17
#define TCS3472_REG_GDATAL           0x18
#define TCS3472_REG_GDATAH           0x19
#define TCS3472_REG_BDATAL           0x1A
#define TCS3472_REG_BDATAH           0x1B

/* TCS3472 Enable Register bits */
#define TCS3472_ENABLE_PON           0x01    // Power ON
#define TCS3472_ENABLE_AEN           0x02    // RGBC Enable
#define TCS3472_ENABLE_WEN           0x08    // Wait Enable
#define TCS3472_ENABLE_AIEN          0x10    // RGBC Interrupt Enable

/* Define the sensor mux channels */
#define MUX_CHANNEL_LINE_SENSOR      1
#define MUX_CHANNEL_OBJECT_SENSOR    2

/* Color definitions */
#define COLOR_UNKNOWN                0
#define COLOR_BLACK                  1
#define COLOR_WHITE                  2
#define COLOR_GREEN                  3
#define COLOR_YELLOW_ORANGE          4
#define COLOR_RED                    5
#define COLOR_BLUE                   6

/* Color calibration structure */
typedef struct {
    uint16_t black_threshold;
    uint16_t white_threshold;
    uint16_t green_ratio_min;
    uint16_t green_ratio_max;
    uint8_t is_calibrated;
} color_config_t;

/* Object color calibration structure */
typedef struct {
    uint16_t white_min_c;

    /* Red color parameters */
    uint16_t red_min_ratio_r_to_g;  // (r/g)*100 ratio threshold
    uint16_t red_min_ratio_r_to_b;  // (r/b)*100 ratio threshold

    /* Blue color parameters */
    uint16_t blue_min_ratio_b_to_r;  // (b/r)*100 ratio threshold
    uint16_t blue_min_ratio_b_to_g;  // (b/g)*100 ratio threshold

    /* Yellow-Orange parameters */
    uint16_t yellow_min_ratio_r_to_b;  // (r/b)*100 ratio threshold
    uint16_t yellow_min_ratio_g_to_b;  // (g/b)*100 ratio threshold
    uint8_t yellow_r_g_diff_percent;   // How close r and g should be (as percentage)
} object_color_config_t;

/* Function prototypes */
uint8_t TCS3472_Init(void);
uint8_t TCS3472_GetID(void);
void TCS3472_Enable(void);
void TCS3472_Disable(void);
void TCS3472_SetIntegrationTime(uint8_t time);
void TCS3472_SetGain(uint8_t gain);
void TCS3472_GetRGBC(uint16_t *r, uint16_t *g, uint16_t *b, uint16_t *c);
Color TCS3472_DetectLineColor(uint16_t r, uint16_t g, uint16_t b, uint16_t c);
void TCS3472_CalibrateColors(void);
void TCS3472_Write(uint8_t reg, uint8_t value);
uint8_t TCS3472_Read8(uint8_t reg);
uint16_t TCS3472_Read16(uint8_t reg);

Color TCS3472_DetectObjectColor(uint16_t r, uint16_t g, uint16_t b, uint16_t c);
void TCS3472_CalibrateObjectColors(void);
void TCS3472_SelectSensor(uint8_t channel);

void init_color_sensors();
void caliberate_color_sensors();

Color TCS3472_DetectRedVsBlue(uint16_t r, uint16_t g, uint16_t b, uint16_t c);
Color TCS3472_DetectWhiteVsYellow(uint16_t r, uint16_t g, uint16_t b, uint16_t c);




/* External variable declarations */
extern color_config_t color_config;
extern object_color_config_t object_color_config;
extern i2c_mux_t mux;
extern UART_HandleTypeDef huart3;
extern I2C_HandleTypeDef hi2c1;
extern uint16_t r_line, g_line, b_line, c_line;
extern uint16_t r_obj, g_obj, b_obj, c_obj;
extern Color line_color, object_color;


#endif /* TCS3472_H */
