PankajaBalasooriya/SLRC-2025-Pulztrones/software/firmware/SLRC2025-Pulztrones/Core/Src/uartcom.c

#include "uartcom.h"
#include "stdio.h"
#include "string.h"
#include "encoders.h"

// UART Initialization function
//void UART_Init(UART_HandleTypeDef *huart)
//{
//    // You can customize this function depending on your UART configuration
//    // Initialize UART with the desired configuration (baud rate, parity, stop bits, etc.)
//    HAL_UART_Init(huart);
//}

// UART Transmit function (send string)
void UART_Transmit(UART_HandleTypeDef *huart, char *data)
{
    // Transmit the string over UART
    HAL_UART_Transmit(huart, (uint8_t *)data, strlen(data), HAL_MAX_DELAY);
}

// UART Transmit function for float (send float formatted as string with customizable header)
void UART_Transmit_Float(UART_HandleTypeDef *huart, const char *header, float number, uint8_t decimal_points)
{
    char buffer[50];  // Buffer to hold the formatted string

    // Format the float value into the buffer with the specified decimal points
    // You can change %.2f to another precision, such as %.3f, %.4f, etc.
    sprintf(buffer, "%s:%.5f\r\n", header, number);  // Use header string as prefix

    // Transmit the formatted string via UART
    HAL_UART_Transmit(huart, (uint8_t *)buffer, strlen(buffer), HAL_MAX_DELAY);
}

// UART Transmit function for integer (send integer formatted as string with customizable header)
void UART_Transmit_Int(UART_HandleTypeDef *huart, const char *header, int number)
{
    char buffer[50];  // Buffer to hold the formatted string

    // Format the integer value into the buffer with the specified header
    sprintf(buffer, "%s:%d\r\n", header, number);

    // Transmit the formatted string via UART
    HAL_UART_Transmit(huart, (uint8_t *)buffer, strlen(buffer), HAL_MAX_DELAY);
}

void UART_Transmit_IR(UART_HandleTypeDef *huart, uint16_t IRL, uint16_t IRR)
{
    char buffer[50];  // Buffer to hold the formatted string

    // Format the float value into the buffer with the specified decimal points
    // You can change %.2f to another precision, such as %.3f, %.4f, etc.
    sprintf(buffer, ">L:%d,R:%d\r\n", IRL, IRR);  // Use header string as prefix
    //sprintf(buffer, "%.2f\t%d\t%d\n", HAL_GetTick() / 1000.0, IRL, IRR);  // Use header string as prefix

    // Transmit the formatted string via UART
    HAL_UART_Transmit(huart, (uint8_t *)buffer, strlen(buffer), HAL_MAX_DELAY);
}

void UART_Transmit_TOF(UART_HandleTypeDef *huart, uint16_t TOF1, uint16_t TOF2, uint16_t TOF3, uint16_t TOF4)
{
    char buffer[50];  // Buffer to hold the formatted string

    // Format the float value into the buffer with the specified decimal points
    // You can change %.2f to another precision, such as %.3f, %.4f, etc.
    sprintf(buffer, ">LW:%d,LC:%d,RC:%d,RW:%d\r\n", TOF1, TOF2, TOF3, TOF4);  // Use header string as prefix

    // Transmit the formatted string via UART
    HAL_UART_Transmit(huart, (uint8_t *)buffer, strlen(buffer), HAL_MAX_DELAY);
}

void UART_Transmit_EncoderData(UART_HandleTypeDef *huart){
	char buffer[50];

	sprintf(buffer, ">D:%.2f,V:%.2f,0:%.2f,W:%.2f\r\n", robot_distance(), robot_speed(), robot_angle(), robot_omega());

	HAL_UART_Transmit(huart, (uint8_t *)buffer, strlen(buffer), HAL_MAX_DELAY);
}
