PankajaBalasooriya/SLRC-2025-Pulztrones/software/firmware/SLRC2025-Pulztrones/Core/Inc/tasks.h

#ifndef TASKS_H
#define TASKS_H

#include <stdint.h>
#include "config.h"


// Task definitions
typedef enum {
    TASK_PLANTATION,
    TASK_MUDDY_ROAD,
	TASK_RAMP,
	NAVIGATE_T0_QR,
	TASK_QR,
    TASK_COLLECTION_POINT,
	TASK_SORTING_POTATOS,
    TASK_OLD_WAREHOUSE,
    TASK_NEW_WAREHOUSE,
    TASK_OUTDOOR,
	TASK_HIDDEN_TASK,
    TASK_NONE // No active task
} TaskType;


// Start a non-blocking delay (delay in milliseconds)
void NonBlockingDelay(uint32_t delay_ms);
// Check if the delay is complete
uint8_t IsDelayComplete(void);


// Function prototypes
void executePlantationTask(void);
void moveToCenterofNextCell();
void moveToCenterofCellinZeroRow();
void moveToCenterofNextCellandNotStop();


void moveToCenterofNextColumnfromFirstRow();
void moveToCenterofNextColumnfromSecondRow();
void moveToCenterofNextColumnfromThiredRow();
void moveTocolumn0Fromcolumn4();

Color picktheBall(uint8_t column, uint8_t row);


void executePotatoSeperationTask(void);




void executeMuddyRoadTask(void);
void executeRampTask(void);
void navigateToQR();
void execteQR();
void executeCollectionPointTask(void);
void executeOldWarehouseTask(void);
void executeNewWarehouseTask(void);
void executeOutdoorTask(void);

// Task manager functions
void selectTask();
void runCurrentTask();

#endif // TASKS_H
