PankajaBalasooriya/SLRC-2025-Pulztrones/software/firmware/SLRC2025-Pulztrones/Core/Src/ballstorage.c

#include "ballstorage.h"

int good_potato_storage; // left
int bad_potato_storage; // right

void init_ball_storage(){
	good_potato_storage = Servo_Register(4, "good_potato_storage", 0, 180, 90);
	Servo_SetAngle(good_potato_storage, 90);

	bad_potato_storage = Servo_Register(5, "bad_potato_storage", 0, 180, 90);
	Servo_SetAngle(bad_potato_storage, 90);
}

void drop_good_potatos(){
	Servo_SetAngle(good_potato_storage, 0);
	HAL_Delay(4000);
	Servo_SetAngle(good_potato_storage, 90);
}

void drop_bad_potatos(){
	Servo_SetAngle(bad_potato_storage, 180);
	HAL_Delay(4000);
	Servo_SetAngle(bad_potato_storage, 90);
}
