PankajaBalasooriya/SLRC-2025-Pulztrones/software/firmware/SLRC2025-Pulztrones/Core/Inc/box_manupilation.h

#ifndef BOX_MANUPILATION_H
#define BOX_MANUPILATION_H

#include <stdint.h>
#include "robot.h"
#include "config.h"
#include "sensors.h"
#include "motion.h"


void box_manupilation();
void box_manupilation_876();
void pickup();
void exit_the_area();
void box_manupilation_630();
void box_manupilation_258();
void box_manupilation_741();

#endif
