PankajaBalasooriya/SLRC-2025-Pulztrones/software/firmware/SLRC2025-Pulztrones/Core/Inc/ballstorage.h

#ifndef BALL_STORAGE_H
#define BALL_STORAGE_H

#include "servo.h"
#include "config.h"

extern int good_potato_storage; // left
extern int bad_potato_storage; // right

void init_ball_storage();
void drop_good_potatos();
void drop_bad_potatos();
#endif
