PankajaBalasooriya/SLRC-2025-Pulztrones/software/firmware/SLRC2025-Pulztrones/Core/Inc/irs.h

/*
 * irs.h
 *
 *  Created on: Apr 1, 2025
 *      Author: PANKAJA
 */

#ifndef INC_IRS_H_
#define INC_IRS_H_

#include "sensors.h"
#include "main.h"
#include "stm32f4xx.h"
#include "analog_mux.h"

typedef enum
{
	IR_FRONT = 0,
	IR_LEFT_FORWARD = 1,
	IR_LEFT_BACK = 2,
	IR_RIGHT_BACK = 3,
	IR_RIGHT_FORWARD = 4
}IR;

typedef struct {
    float a;
    float b;
    float c;
} IR_Calibration_t;


void analogReadIRs(void);
uint16_t readRawIR(IR ir);
uint16_t getIRDistance(IR ir, uint16_t raw);

#endif /* INC_IRS_H_ */
